PhobGCC/PhobGCC-doc/For_Makers/BoardPics/1.2.1_BackWithBracket.jpg

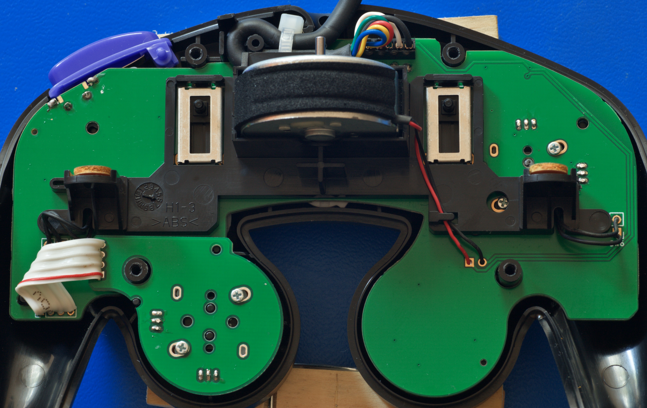
For_Makers/BoardPics/1.2.1_BackWithBracket.jpg
