PhobGCC/PhobGCC-doc/For_Makers/BuildPics_1.2.2/CVAC1049_gmOXOu2-output.jpg

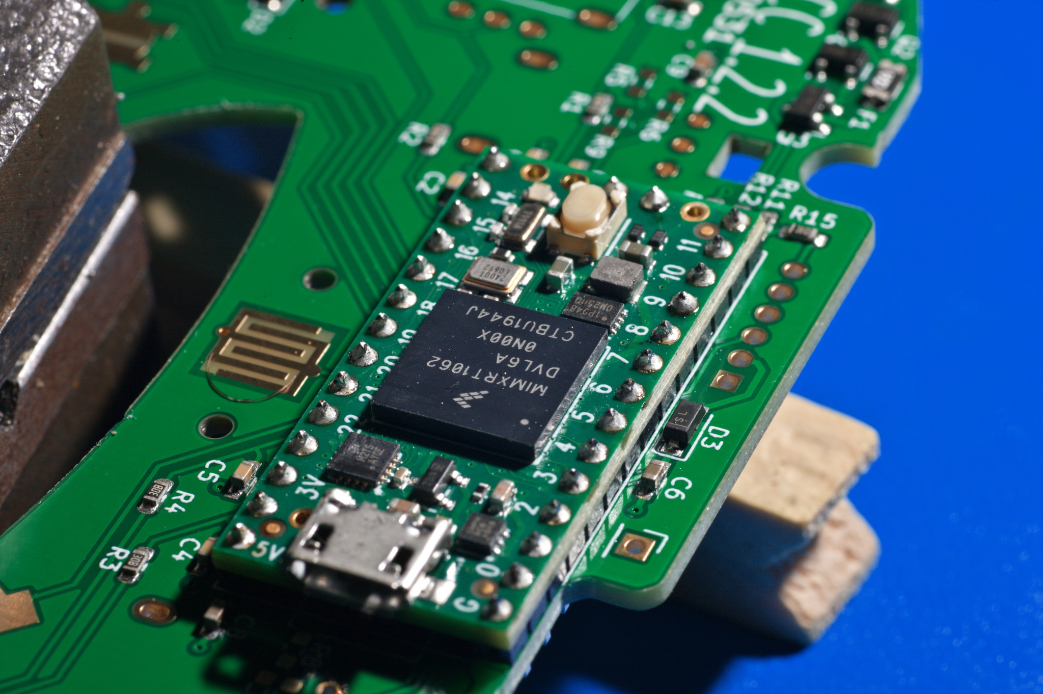
For_Makers/BuildPics_1.2.2/CVAC1049_gmOXOu2-output.jpg
