PhobGCC/PhobGCC-doc/For_Makers/BuildPics_1.2.2/CVAC1091_yIpYOPa-output.jpg

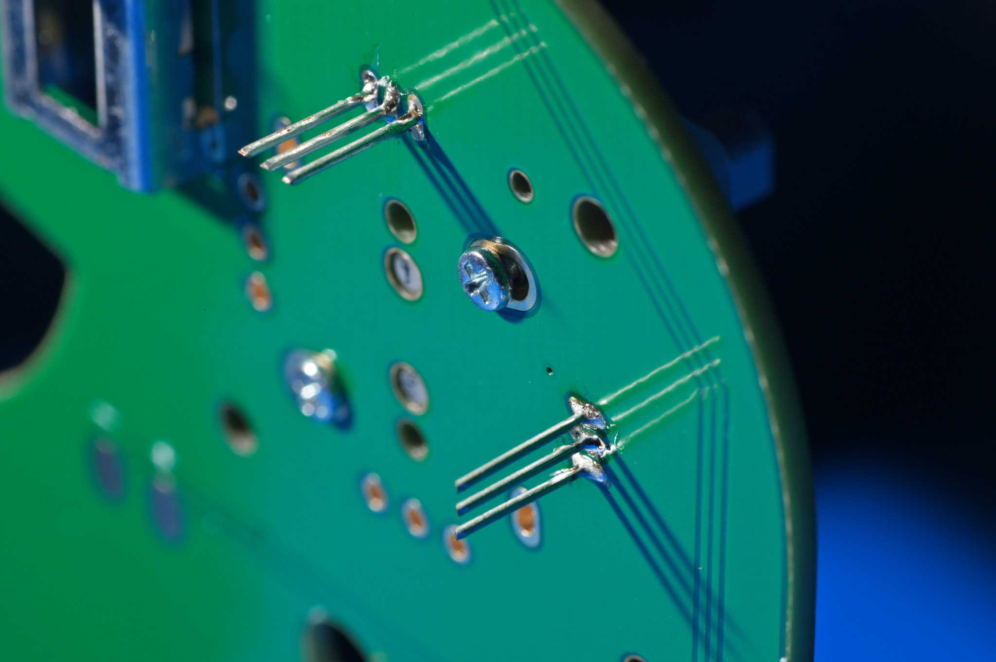
For_Makers/BuildPics_1.2.2/CVAC1091_yIpYOPa-output.jpg
