PhobGCC/PhobGCC-doc/For_Users/Phob_Buying_Guide_Images/badhalljoints_full.jpg

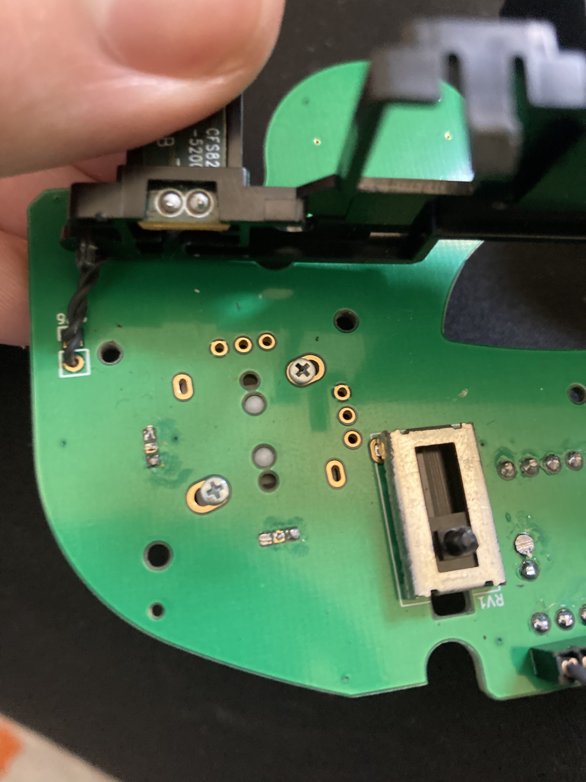
For_Users/Phob_Buying_Guide_Images/badhalljoints_full.jpg
