PhobGCC/PhobGCC-doc/For_Users/Phob_Buying_Guide_Images/Phob1.0_TopView.jpeg

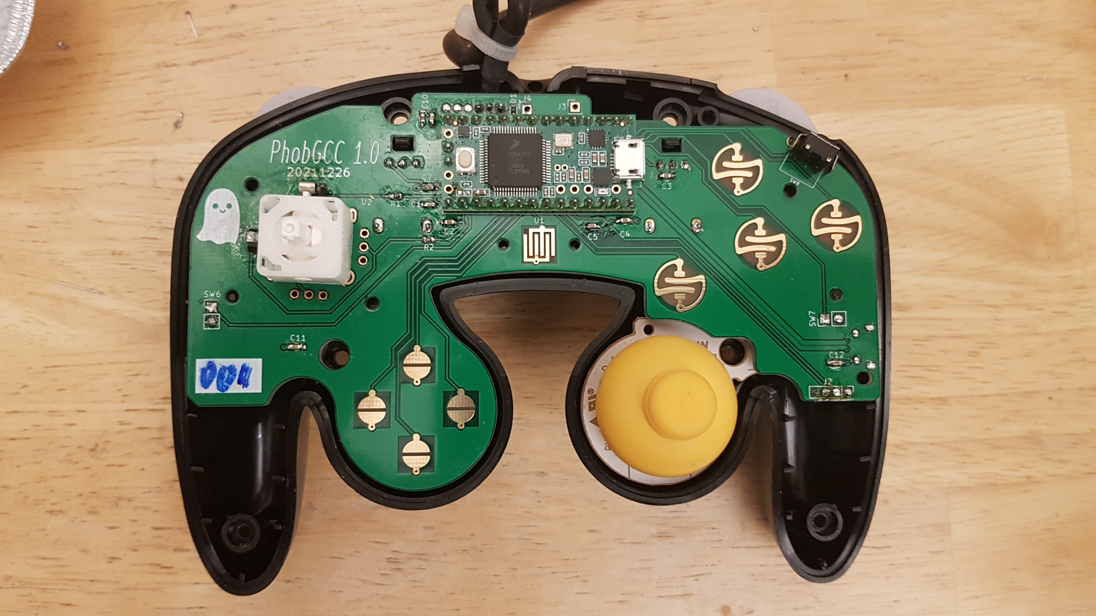
For_Users/Phob_Buying_Guide_Images/Phob1.0_TopView.jpeg
