PhobGCC/PhobGCC-doc/For_Users/Phob_Buying_Guide_Images/Phob1.1_TopView.jpeg

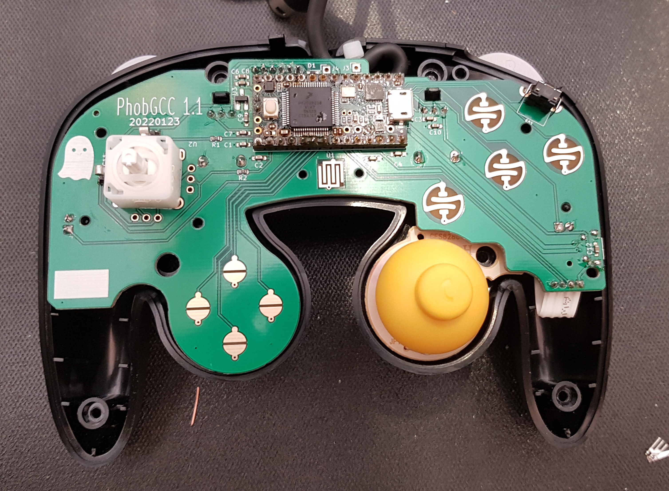
For_Users/Phob_Buying_Guide_Images/Phob1.1_TopView.jpeg
